lowvoltage/USBTinyISP-Single-Sided/PCB_v0.01.png

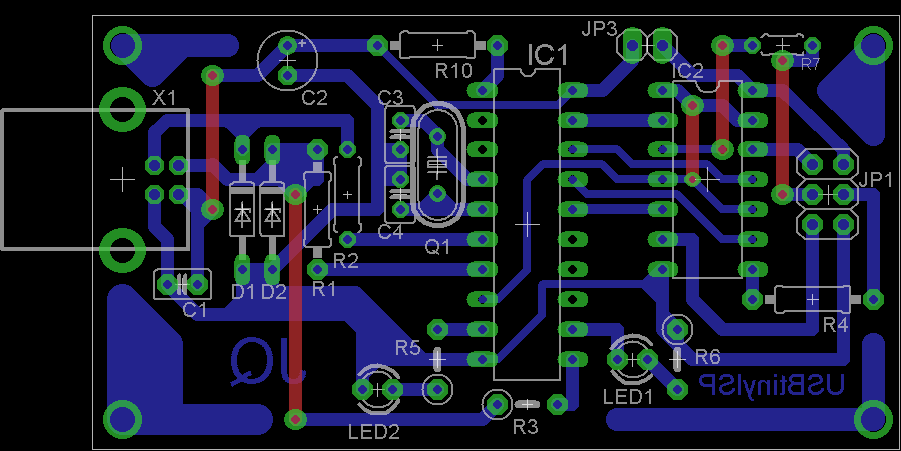
PCB_v0.01.png
