lowvoltage/USBTinyISP-Single-Sided/PCB_v0.04.png

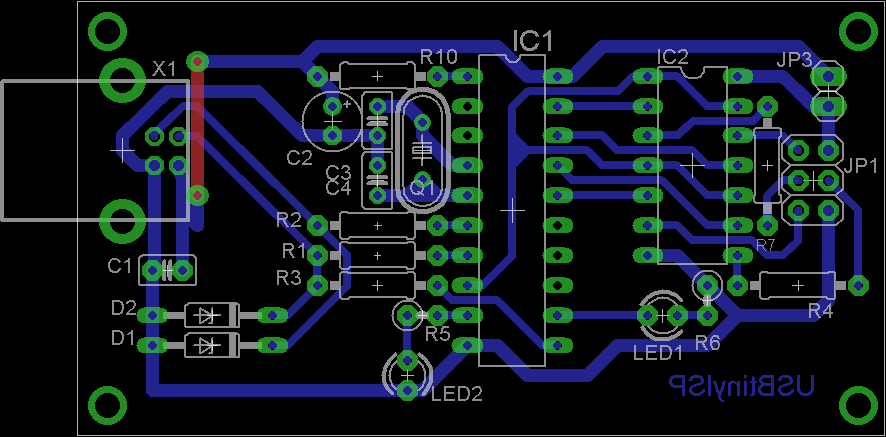
PCB_v0.04.png
