lowvoltage/USBTinyISP-Single-Sided/PCB_v0.09.png

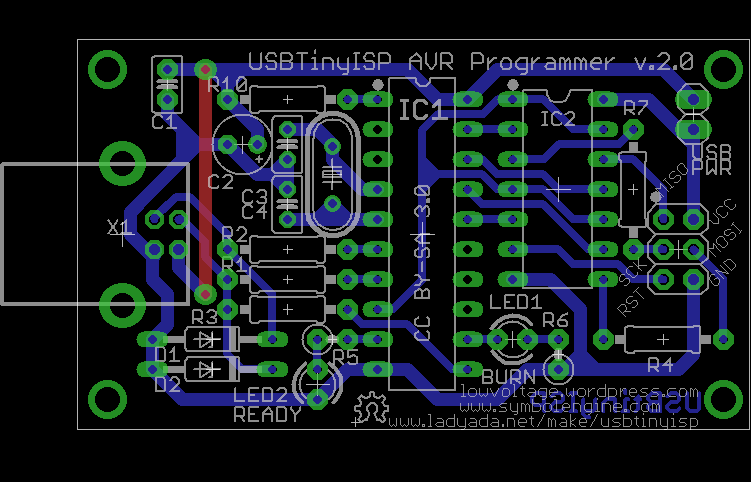
PCB_v0.09.png
