lowvoltage/USBTinyISP-Single-Sided/PCB_v0.10.png

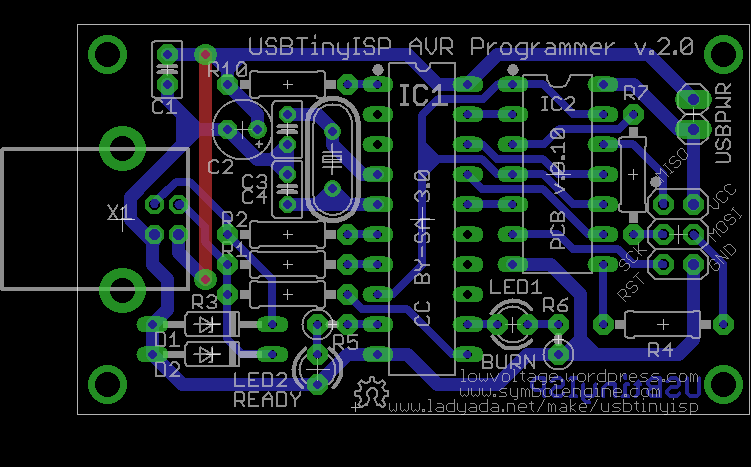
PCB_v0.10.png
